slomkowski/szark/firmware/bridge/motor_driver.cpp

/*
 * motor_driver.cpp
 *
 *  Created on: 05-08-2013
 *      Author: michal
 */

#include "global.hpp"
#include "motor_driver.hpp"
#include "i2c.hpp"

static const uint8_t MOTOR_DRIVER_ADDRESS = 0x12;

using namespace motor;

static uint8_t get(uint8_t command, uint8_t motor) {
	uint8_t val;

	i2c::start();

	i2c::write(i2c::addressToWrite(MOTOR_DRIVER_ADDRESS));
	i2c::write(command);
	i2c::write(motor);

	i2c::start();
	i2c::write(i2c::addressToRead(MOTOR_DRIVER_ADDRESS));

	val = i2c::read(i2c::NACK);

	i2c::stop();

	return val;
}

static void set(uint8_t command, uint8_t motor, uint8_t value) {
	i2c::start();

	i2c::write(i2c::addressToWrite(MOTOR_DRIVER_ADDRESS));
	i2c::write(command);
	i2c::write(motor);
	i2c::write(value);

	i2c::stop();
}

void motor::brake() {
	i2c::start();

	i2c::write(i2c::addressToWrite(MOTOR_DRIVER_ADDRESS));
	i2c::write(BRAKE);

	i2c::stop();
}

motor::Direction motor::getDirection(motor::Motor motor) {
	return (Direction) get(GET_DIRECTION, motor);
}

void motor::setDirection(motor::Motor motor, motor::Direction direction) {
	set(SET_DIRECTION, motor, (uint8_t) direction);
}

uint8_t motor::getSpeed(motor::Motor motor) {
	return get(GET_SPEED, motor);
}

void motor::setSpeed(motor::Motor motor, uint8_t speed) {
	set(SET_SPEED, motor, speed);
}
