slomkowski/szark/client/desktop_client/src/main/java/eu/slomkowski/szark/client/status/MotorSet.java

package eu.slomkowski.szark.client.status;

import com.google.gson.annotations.Expose;
import com.google.gson.annotations.SerializedName;
import eu.slomkowski.szark.client.HardcodedConfiguration;

public class MotorSet extends AbstractMotor {

    @Expose
    @SerializedName("l")
    public Motor left = new Motor();

    @Expose
    @SerializedName("r")
    public Motor right = new Motor();

    @Override
    public boolean equals(Object obj) {
        if (obj == null) {
            return false;
        }
        if (obj == this) {
            return true;
        }

        if (obj instanceof MotorSet) {
            final MotorSet o = (MotorSet) obj;
            if (left.equals(o.left) && right.equals(o.right)) {
                return true;
            }
        }

        return false;
    }

    @Override
    public synchronized void setSpeedLimit(byte speed) {
        if (speed < 0) {
            speedLimit = 0;
        } else if (speed > HardcodedConfiguration.MOTOR_SPEED_MAX) {
            speedLimit = HardcodedConfiguration.MOTOR_SPEED_MAX;
        } else {
            speedLimit = speed;
        }

        left.setSpeedLimit(speedLimit);
        right.setSpeedLimit(speedLimit);
    }

    @Override
    public void stop() {
        left.stop();
        right.stop();
    }

    public class Motor extends AbstractParams {
    }
}
