slomkowski/szark/firmware/motor_driver/pwm.cpp

#include "global.h"

#include <avr/io.h>
#include <inttypes.h>
#include <avr/interrupt.h>
#include <util/delay.h>
#include <avr/cpufunc.h>
#include <avr/pgmspace.h>

#include <stdlib.h>

#include "pwm.h"

// interrupt interval - the base is (f_clk/1024) ~= 0.25ms
// current setting - one interrupt per 125ms
#define TIMER_INTERVAL 500

using namespace motor;

/*
 * in my application, the maximal controlled speed was limited to 92 impulses per interrupt
 * this is the table of valid speeds (number of impulses in TIMER_INTERVAL time).
 * Maximal speed is limited to 11 TODO dokumentacja motor driver prędkości
 */

const uint8_t s_vals[] PROGMEM = { 0, 10, 20, 28, 36, 46, 54, 66, 74, 84, 92, 255 };
const uint8_t m1_speeds[] PROGMEM = { 0, 40, 50, 60, 75, 100, 130, 160, 180, 200, 230, 255 };
const uint8_t m2_speeds[] PROGMEM = { 0, 65, 75, 90, 100, 125, 150, 170, 190, 215, 240, 255 };

namespace motor {
	Motor motor1;
	Motor motor2;
}

static void pwm1_start_generating() {
	TCCR0A |= (1 << COM0A1);
	motor1.counter = 0;
	GIMSK |= (1 << INT0);
}

static void pwm1_stop_generating() {
	TCCR0A &= ~(1 << COM0A1);
	GIMSK &= ~(1 << INT0);
}

static void pwm2_start_generating() {
	TCCR0A |= (1 << COM0B1);
	motor2.counter = 0;
	GIMSK |= (1 << INT1);
}

static void pwm2_stop_generating() {
	TCCR0A &= ~(1 << COM0B1);
	GIMSK &= ~(1 << INT1);
}

void motor::init() {
	// set outputs
	DDR(MOTOR1_PORT) |= (1 << MOTOR1_FORWARD_PIN) | (1 << MOTOR1_BACKWARD_PIN) | (1 << MOTOR1_PWM_PIN);
	DDR(MOTOR2_PORT) |= (1 << MOTOR2_FORWARD_PIN) | (1 << MOTOR2_BACKWARD_PIN) | (1 << MOTOR2_PWM_PIN);

	//set encoders inputs & pullups
	DDR(ENCODER_PORT) &= ~(1 << ENCODER1_PIN) & ~(1 << ENCODER2_PIN);
	PORT(ENCODER_PORT) |= (1 << ENCODER1_PIN) | (1 << ENCODER2_PIN);

	// brake motors
	setDirection(MOTOR1_IDENTIFIER, MOTOR_STOP);
	setDirection(MOTOR2_IDENTIFIER, MOTOR_STOP);

	// pwm setup
	TCCR0A = (1 << WGM00); // phase-correct
	TCCR0B = (1 << CS01) | (1 << CS00); // prescaler clkio/64

	// external interrupts setup - for encoders support
	MCUCR |= (1 << ISC10) | (1 << ISC00); // enable interrupts at both rising and falling edges

	// setup of the interrupt timer,
	// Timer1 -- CTC mode, enable overflow interrupt, prescaler f_clk/1024
	TCCR1A = 0;
	TCCR1B = (1 << WGM12) | (1 << CS12) | (1 << CS10);

	TIMSK |= (1 << OCIE1A);
	OCR1A = TIMER_INTERVAL;
}

// returned value is the actual PWM setting, which changes by encoder feedback, not the one set by the user
uint8_t motor::getSpeed(uint8_t motor) {
	if (motor == MOTOR1_IDENTIFIER) {
		return PWM1_REG ;
	} else {
		return PWM2_REG ;
	}
}

uint8_t motor::getDirection(uint8_t motor) {
	if (motor == MOTOR1_IDENTIFIER) {
		return (motor1.direction);
	} else {
		return (motor2.direction);
	}
}

void motor::setSpeed(uint8_t motor, uint8_t speed) {
	if (motor == MOTOR1_IDENTIFIER) {
#if DEBUG
		if(speed == '0') motor1.refSpeed = pgm_read_byte(&(s_vals[0]));
		else if(speed == 'm') motor1.refSpeed = pgm_read_byte(&(s_vals[11]));
		else
#endif
		motor1.refSpeed = pgm_read_byte(&(s_vals[speed % 12]));
	} else {
#if DEBUG
		if(speed == '0') motor2.refSpeed = pgm_read_byte(&(s_vals[0]));
		else if(speed == 'm') motor2.refSpeed =pgm_read_byte(&(s_vals[11]));
		else
#endif
		motor2.refSpeed = pgm_read_byte(&(s_vals[speed % 12]));
	}
}

void motor::setDirection(uint8_t motor, uint8_t direction) {
	// motor 1
	if (motor == MOTOR1_IDENTIFIER) {
		if (direction == MOTOR_FORWARD) {
			PORT(MOTOR1_PORT) |= (1 << MOTOR1_FORWARD_PIN);
			PORT(MOTOR1_PORT) &= ~(1 << MOTOR1_BACKWARD_PIN);

			pwm1_start_generating();
			motor1.direction = FORWARD;
		} else if (direction == MOTOR_BACKWARD) {
			PORT(MOTOR1_PORT) &= ~(1 << MOTOR1_FORWARD_PIN);
			PORT(MOTOR1_PORT) |= (1 << MOTOR1_BACKWARD_PIN);

			pwm1_start_generating();
			motor1.direction = BACKWARD;
		} else {
			PORT(MOTOR1_PORT) |= (1 << MOTOR1_FORWARD_PIN);
			PORT(MOTOR1_PORT) |= (1 << MOTOR1_BACKWARD_PIN);

			pwm1_stop_generating();
			motor1.direction = STOP;
		}
	} else // motor 2
	{
		if (direction == MOTOR_FORWARD) {
			PORT(MOTOR2_PORT) |= (1 << MOTOR2_FORWARD_PIN);
			PORT(MOTOR2_PORT) &= ~(1 << MOTOR2_BACKWARD_PIN);

			pwm2_start_generating();
			motor2.direction = FORWARD;
		} else if (direction == MOTOR_BACKWARD) {
			PORT(MOTOR2_PORT) &= ~(1 << MOTOR2_FORWARD_PIN);
			PORT(MOTOR2_PORT) |= (1 << MOTOR2_BACKWARD_PIN);

			pwm2_start_generating();
			motor2.direction = BACKWARD;
		} else {
			PORT(MOTOR2_PORT) |= (1 << MOTOR2_FORWARD_PIN);
			PORT(MOTOR2_PORT) |= (1 << MOTOR2_BACKWARD_PIN);

			pwm2_stop_generating();
			motor2.direction = STOP;
		}
	}
}

ISR(ENCODER1_INTERRUPT) {
	motor1.counter++;
}

ISR(ENCODER2_INTERRUPT) {
	motor2.counter++;
}
