slomkowski/szark/server/common_lib/src/Configuration.cpp

#include "Configuration.hpp"

#include <boost/property_tree/ptree.hpp>
#include <boost/property_tree/ini_parser.hpp>

using namespace common::config;

WALLAROO_REGISTER(Configuration, std::vector<std::string>)
WALLAROO_REGISTER(Configuration)

namespace common {
    namespace config {
        struct ConfigurationImpl {
            boost::property_tree::ptree ptree;
        };

        template<typename TYPE>
        TYPE get(boost::property_tree::ptree tree, const std::string &property) {
            try {
                return tree.get<TYPE>(property);
            } catch (boost::property_tree::ptree_bad_path) {
                throw ConfigException(std::string(typeid(TYPE).name()) + " key \'" + property + "\' not found");
            }
        }
    }
}

common::config::Configuration::Configuration()
        : impl(new ConfigurationImpl()) { }

common::config::Configuration::Configuration(const std::string fileName)
        : impl(new ConfigurationImpl()) {
    boost::property_tree::read_ini(fileName, impl->ptree);
}

common::config::Configuration::Configuration(std::vector<std::string> const fileNames)
        : impl(new ConfigurationImpl()) {
    for (auto &name : fileNames) {
        boost::property_tree::read_ini(name, impl->ptree);
    }
}

common::config::Configuration::~Configuration() {
    delete impl;
}

int common::config::Configuration::getInt(const std::string &property) {
    return get<int>(impl->ptree, property);
}

bool common::config::Configuration::getBool(const std::string &property) {
    return get<bool>(impl->ptree, property);
}

std::string common::config::Configuration::getString(const std::string &property) {
    return get<std::string>(impl->ptree, property);
}

void common::config::Configuration::putInt(const std::string &property, const int val) {
    impl->ptree.put(property, val);
}

void common::config::Configuration::putBool(const std::string &property, const bool val) {
    impl->ptree.put(property, val);
}

void common::config::Configuration::putString(const std::string &property, const std::string val) {
    impl->ptree.put(property, val);
}
