slomkowski/szark/server/common_lib/include/DataHolder.hpp

#pragma once

#include <boost/utility/enable_if.hpp>

#include "usb-commands.hpp"

#include <typeinfo>
#include <cstring>
#include <vector>
#include <memory>

namespace common {
    namespace bridge {

        constexpr int DATAHOLDER_MAX_DATA_SIZE = 40;

        /**
        * Helpful class used by Interface class to hold each USB request. The class is immutable, only data can change.
        */
        class DataHolder {
        public:
            /**
             * Creates empty request.
             */
            DataHolder();

            /**
            * Creates single-byte request.
            * @param request
            * @param pr priority of the request
            */
            DataHolder(const USBCommands::Request request, const int pr, bool killswitchDependent);

            /**
            * Creates two-byte request.
            * @param request
            * @param pr priority of the request
            * @param d
            */
            DataHolder(const USBCommands::Request request, const int pr, bool killswitchDependent, const uint8_t byte);

            DataHolder(const DataHolder &dh);

            /**
            * Creates the request from the given structure. The structure content is copied byte by byte.
            * @param request
            * @param pr priority of the request
            * @param structure any data type except std::vector.
            */
            template<typename TYPE,
                    typename = typename std::enable_if<not std::is_same<TYPE, std::vector<uint8_t>>::value>::type>
            DataHolder(const USBCommands::Request request, const int pr, bool killswitchDependent, TYPE &structure) {
                static_assert(DATAHOLDER_MAX_DATA_SIZE >= sizeof(TYPE) + 1,
                              "Should be at least of the size of the structure.");

                initData(request, pr, killswitchDependent, sizeof(TYPE));

                std::memcpy(this->_data + 1, &structure, sizeof(TYPE));
            }

            DataHolder(const USBCommands::Request request, const int pr, bool killswitchDependent, void *data,
                       int size);

            /**
            * Creates the request from the vector of bytes. The vector's data is copied into request.
            * @param request
            * @param pr priority of the request
            * @param vec
            */
            DataHolder(const USBCommands::Request request, const int pr, bool killswitchDependent,
                       const std::vector<uint8_t> &vec);

            DataHolder &operator=(const DataHolder &dh);

            /**
            * Returns the contained data along with the request number.
            * @return pointer to the stored data.
            */
            const uint8_t *getPlainData() const {
                return _data;
            }

            /**
            * Returns the pointer to the payload (all data except USB request number) casted on the type given.
            * @return
            */
            template<typename TYPE>
            TYPE *getPayload() const {
                return reinterpret_cast<TYPE *>(_data + 1);
            }

            USBCommands::Request getRequest() const {
                return static_cast<const USBCommands::Request>(_data[0]);
            }

            unsigned int getSize() const {
                return _length;
            }

            int getPriority() const {
                return _priority;
            }

            bool isKillSwitchDependent() const {
                return _killswitchDependent;
            }

            /**
            * Appends data to the given vector instance.
            * @param vec existing std::vector<uint8_t> instance.
            */
            void appendTo(std::vector<uint8_t> &vec) const {
                vec.insert(vec.end(), _data, _data + _length);
            }

            /**
            * Checks if the object is equal to the given one.
            * @param right
            * @return
            */
            bool equals(const DataHolder &right);

        private:
            mutable uint8_t _data[DATAHOLDER_MAX_DATA_SIZE];
            unsigned int _length = 0;
            int _priority = 0;
            bool _killswitchDependent = false;

            static_assert(DATAHOLDER_MAX_DATA_SIZE >= 2, "Should be at least one byte.");

            void initData(USBCommands::Request request, const int pr, bool killswitchDependent, unsigned int dataSize);
        };

        class DataHolderComparer {
        public:
            bool operator()(DataHolder &lhs, DataHolder &rhs) const {
                return lhs.getPriority() > rhs.getPriority();
            }
        };
    }
}
