slomkowski/szark/firmware/bridge/LUFAConfig.h

/*
 LUFA Library
 Copyright (C) Dean Camera, 2014.

 dean [at] fourwalledcubicle [dot] com
 www.lufa-lib.org
 */

/*
 Copyright 2014  Dean Camera (dean [at] fourwalledcubicle [dot] com)

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
 The author disclaims all warranties with regard to this
 software, including all implied warranties of merchantability
 and fitness.  In no event shall the author be liable for any
 special, indirect or consequential damages or any damages
 whatsoever resulting from loss of use, data or profits, whether
 in an action of contract, negligence or other tortious action,
 arising out of or in connection with the use or performance of
 this software.
 */

/** \file
 *  \brief LUFA Library Configuration Header File
 *
 *  This header file is used to configure LUFA's compile time options,
 *  as an alternative to the compile time constants supplied through
 *  a makefile.
 *
 *  For information on what each token does, refer to the LUFA
 *  manual section "Summary of Compile Tokens".
 */

#ifndef _LUFA_CONFIG_H_
#define _LUFA_CONFIG_H_

/* USB Class Driver Related Tokens: */
//		#define HID_HOST_BOOT_PROTOCOL_ONLY
//		#define HID_STATETABLE_STACK_DEPTH       {Insert Value Here}
//		#define HID_USAGE_STACK_DEPTH            {Insert Value Here}
//		#define HID_MAX_COLLECTIONS              {Insert Value Here}
//		#define HID_MAX_REPORTITEMS              {Insert Value Here}
//		#define HID_MAX_REPORT_IDS               {Insert Value Here}
//		#define NO_CLASS_DRIVER_AUTOFLUSH
/* General USB Driver Related Tokens: */
//		#define ORDERED_EP_CONFIG
#define USE_STATIC_OPTIONS               (USB_DEVICE_OPT_FULLSPEED | USB_OPT_REG_ENABLED | USB_OPT_AUTO_PLL)
#define USB_DEVICE_ONLY
//		#define USB_HOST_ONLY
//		#define USB_STREAM_TIMEOUT_MS            {Insert Value Here}
//		#define NO_LIMITED_CONTROLLER_CONNECT
//		#define NO_SOF_EVENTS

/* USB Device Mode Driver Related Tokens: */
//		#define USE_RAM_DESCRIPTORS
#define USE_FLASH_DESCRIPTORS
//		#define USE_EEPROM_DESCRIPTORS
//		#define NO_INTERNAL_SERIAL
#define FIXED_CONTROL_ENDPOINT_SIZE      8
//		#define DEVICE_STATE_AS_GPIOR            {Insert Value Here}
#define FIXED_NUM_CONFIGURATIONS         1
//		#define CONTROL_ONLY_DEVICE
//		#define INTERRUPT_CONTROL_ENDPOINT
//		#define NO_DEVICE_REMOTE_WAKEUP
//		#define NO_DEVICE_SELF_POWER

/* USB Host Mode Driver Related Tokens: */
//		#define HOST_STATE_AS_GPIOR              {Insert Value Here}
//		#define USB_HOST_TIMEOUT_MS              {Insert Value Here}
//		#define HOST_DEVICE_SETTLE_DELAY_MS	     {Insert Value Here}
//		#define NO_AUTO_VBUS_MANAGEMENT
//		#define INVERTED_VBUS_ENABLE_LINE
#endif
