slomkowski/szark/server/control_server/src/NetServer.hpp

#pragma once

#include "RequestQueuer.hpp"
#include "Configuration.hpp"
#include "IoServiceProvider.hpp"

#include <log4cpp/Category.hh>
#include <wallaroo/registered.h>
#include <boost/asio.hpp>

#include <string>
#include <memory>
#include <unordered_map>
#include <stdexcept>

namespace processing {

    class NetException : public std::runtime_error {
    public:
        NetException(const std::string &message)
                : std::runtime_error(message) {
        }
    };

    class INetServer {
    public:
        virtual void sendResponse(long id, std::string response, bool transmit) = 0;

        virtual ~INetServer() = default;
    };

    class NetServer : public wallaroo::Part, public INetServer {
    public:
        NetServer();

        NetServer(unsigned int port);

        virtual void sendResponse(long id, std::string response, bool transmit);

        virtual ~NetServer();

    private:
        log4cpp::Category &logger;

        wallaroo::Collaborator<common::config::Configuration> config;
        wallaroo::Collaborator<IRequestQueuer> reqQueuer;
        wallaroo::Collaborator<common::IoServiceProvider> ioServiceProvider;

        std::unique_ptr<boost::asio::ip::udp::socket> udpSocket;
        boost::asio::ip::udp::endpoint recvSenderEndpoint;

        std::unordered_map<long, boost::asio::ip::udp::endpoint> sendersMap;

        unsigned int udpPort;

        std::unique_ptr<char> buff;

        void Init();

        void doReceive();

        void removeFromRequestMap(long id);
    };

} /* namespace processing */
