slomkowski/szark/server/control_server/src/DataHolder.cpp

#include <cstring>

#include "DataHolder.hpp"

using namespace bridge;

bridge::DataHolder::DataHolder(const USBCommands::Request request, const int pr, bool killswitchDependent) {
	initData(request, pr, killswitchDependent, 0);
}

bridge::DataHolder::DataHolder(const USBCommands::Request request, const int pr, bool killswitchDependent,
		const uint8_t byte) {
	initData(request, pr, killswitchDependent, sizeof(char));

	data[1] = byte;
}

bridge::DataHolder::DataHolder(const USBCommands::Request request, const int pr, bool killswitchDependent,
		const std::vector<uint8_t> &vec) {
	initData(request, pr, killswitchDependent, vec.size());

	unsigned int idx = 1;
	for (auto &val : vec) {
		data[idx] = val;
		idx++;
	}
}

bridge::DataHolder::DataHolder(const DataHolder &dh) {
	this->length = dh.length;
	this->priority = dh.priority;
	this->killswitchDependent = dh.killswitchDependent;
	std::memcpy(this->data, dh.data, length + 1);
}

bridge::DataHolder::DataHolder(const USBCommands::Request request, const int pr, bool killswitchDependent, void *data,
		int size) {
	initData(request, pr, killswitchDependent, size);
	std::memcpy(this->data + 1, data, length);
}

DataHolder &bridge::DataHolder::operator=(const DataHolder &dh) {
	this->length = dh.length;
	this->priority = dh.priority;
	this->killswitchDependent = dh.killswitchDependent;
	std::memcpy(this->data, dh.data, length + 1);

	return *this;
}

bool bridge::DataHolder::equals(const DataHolder &right) {

	if (this->priority != right.priority) {
		return false;
	}

	if (this->length != right.length) {
		return false;
	}

	if (this->killswitchDependent != right.killswitchDependent) {
		return false;
	}

	if (std::memcmp(this->data, right.data, this->length + 1) != 0) {
		return false;
	}

	return true;
}

void bridge::DataHolder::initData(USBCommands::Request request, const int pr, bool killswitchDependent,
		unsigned int dataSize) {
	priority = pr;
	length = dataSize + 1;
	data[0] = request;
	this->killswitchDependent = killswitchDependent;
}
