slomkowski/szark/firmware/bridge/killswitch.hpp

/*
 * killswitch.h
 *
 *  Created on: 08-08-2013
 *      Author: michal
 */

#ifndef KILLSWITCH_H_
#define KILLSWITCH_H_

namespace killswitch {

void init();

void setActive(bool active);

bool isActive();

bool isCausedByHardware();

bool isCausedBySoftware();

/**
 * This function should be called in the main loop to monitor hardware kill switch sources.
 */
void checkHardware();

}

#endif /* KILLSWITCH_H_ */
