slomkowski/szark/firmware/bridge/expander.hpp

/*
 * expander.h
 *
 *  Created on: 06-08-2013
 *      Author: michal
 */

#ifndef EXPANDER_H_
#define EXPANDER_H_

namespace expander {
	void setValue(uint8_t data);
	uint8_t getValue();
}

#endif /* EXPANDER_H_ */
