slomkowski/szark/server/camera_server/example-config.ini

[ImageGrabber]
left_device = 0
left_width = 352
left_height = 288

right_device = 1
right_width = 352
right_height = 288

head_device = 0
head_width = 720
head_height = 480

[HeadImageSource]
loglevel = NOTICE
input_gripper_no = 0
input_back_no = 1

[V4LImageGrabber]
loglevel = NOTICE

[TurboJpegEncoder]
loglevel = NOTICE

[OpenCvJpegEncoder]
loglevel = NOTICE

[NetworkServer]
loglevel = NOTICE
enable_ipv6 = true
port = 10192
