slomkowski/szark/server/camera_server/test/GripperImageSourceTest.cpp

#include "CameraImageGrabber.hpp"
#include "GripperImageSource.hpp"

#include <boost/test/unit_test.hpp>
#include <wallaroo/catalog.h>

using namespace std;
using namespace camera;

BOOST_AUTO_TEST_CASE(GripperImageSourceTest_Run) {
    wallaroo::Catalog catalog;
    catalog.Create("imgGrabberLeft", "ImageGrabber", string("left"));
    catalog.Create("imgGrabberRight", "ImageGrabber", string("right"));
    catalog.Create("imgCombiner", "GripperImageSource");
    catalog.Create("hudPainter", "GripperHudPainter");

    wallaroo::use(catalog["imgGrabberLeft"]).as("leftCameraGrabber").of(catalog["imgCombiner"]);
    wallaroo::use(catalog["imgGrabberRight"]).as("rightCameraGrabber").of(catalog["imgCombiner"]);
    wallaroo::use(catalog["hudPainter"]).as("hudPainter").of(catalog["imgCombiner"]);

    catalog.CheckWiring();

    shared_ptr<IImageSource> imageGrabber = catalog["imgCombiner"];

    this_thread::sleep_for(chrono::milliseconds(100));

    for (int i = 0; i < 10; i++) {
        string fileName = "out.jpg";
        string sourceName = "default";
        auto result = imageGrabber->getImage(sourceName, true);
        cv::imwrite(fileName, result);
        BOOST_TEST_MESSAGE("Frame combined and saved to " << fileName);
    }

    BOOST_CHECK_EQUAL(1, 1);
}
